fairdevices/cad/src/elec/WaMaControl/spice/powersupply.asc

C1: cap; 10n; Rpar=1e12
C2: cap; 1000n; Rpar=1e12
C3: cap; 1000n; Rpar=1e12
C4: cap; 100µ; Rpar=1e12
D1: diode; 1N914
D2: diode; 1N914
D3: diode; 1N914
D4: diode; 1N914
L1: ind2; 1; Rser=10m Rpar=1e12
L2: ind2; 1; Rser=10m Rpar=1e12
R1: EuropeanResistor; 400
R2: EuropeanResistor; 400
R3: EuropeanResistor; 400
R4: EuropeanResistor; 400
R5: EuropeanResistor; 400
V1: voltage; SINE(0 {1.41*9*1.1} 50)
Named nets: 0
K1 L1 L2 0.999
.tran 100m
Valve-cold
Valve-warm
Pump
Heating
